gvoigtlaender/EspFanControl/fw/src/config.h

#ifndef SRC_CONFIG_H_
#define SRC_CONFIG_H_

/* Copyright 2018 Georg Voigtlaender gvoigtlaender@googlemail.com */
#define WLAN_SSID "S59WLAN"
#define WLAN_PASSWD "finqku-120-jt"

#endif // SRC_CONFIG_H_
